OpenhimerLab/CareLite-GPIB/HW/MultiTemp/MultiTemp.png

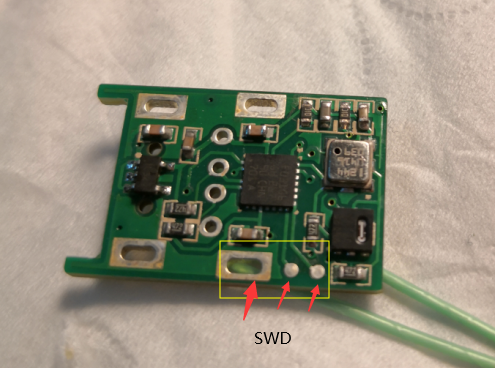
HW/MultiTemp/MultiTemp.png
