OpenhimerLab/CareLite-GPIB/PC Software 1.png

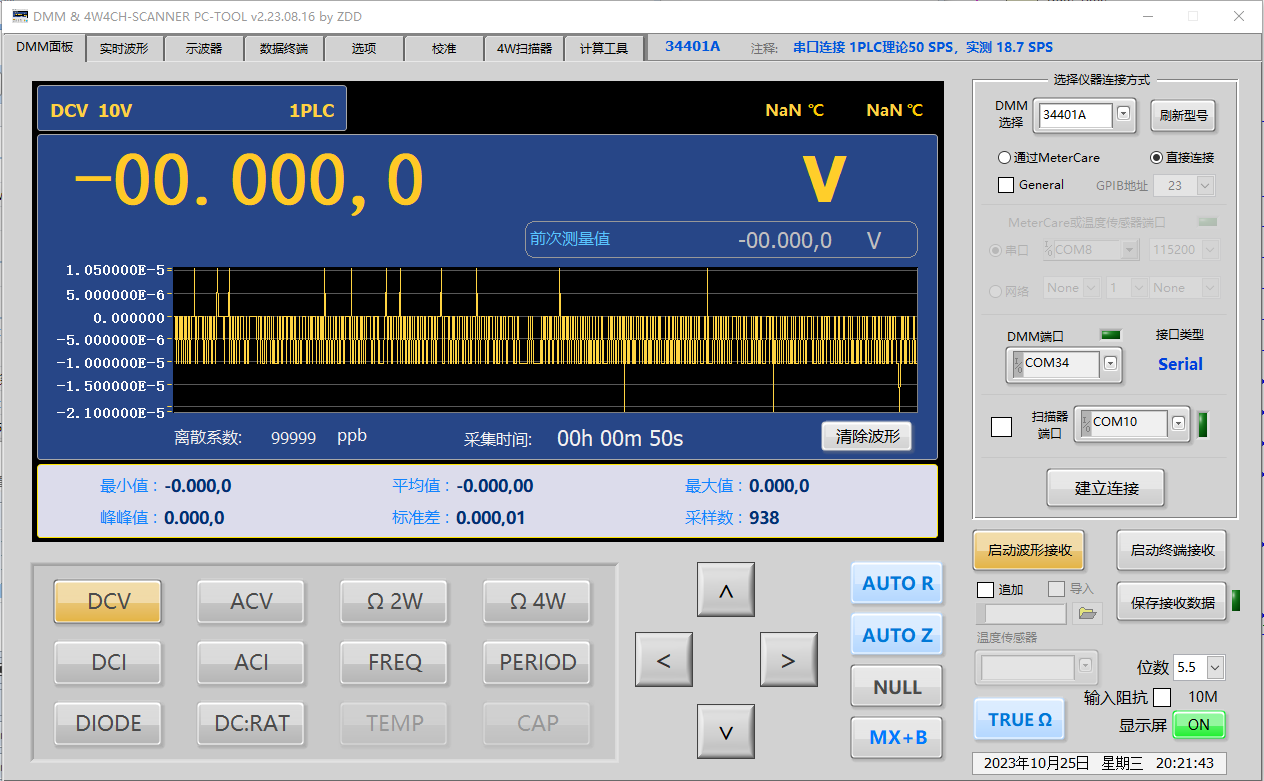
PC Software 1.png
