OpenhimerLab/CareLite-GPIB/PCB4.png

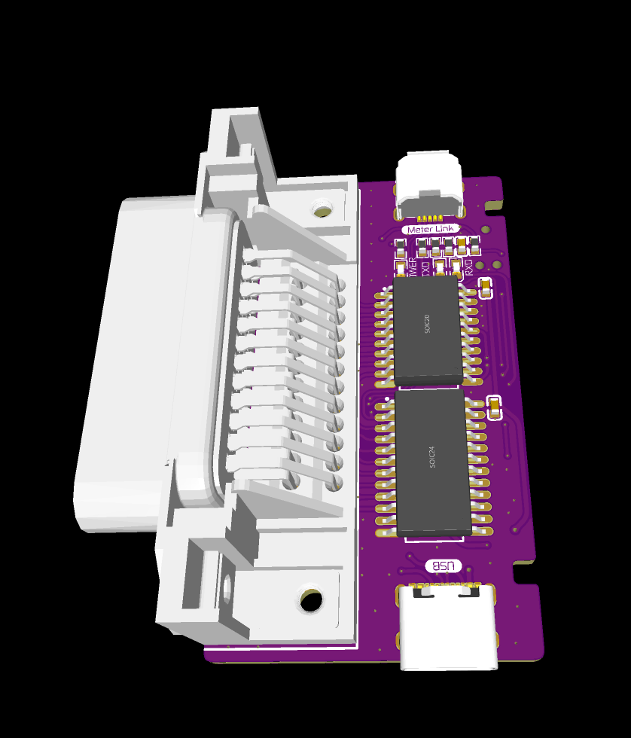
PCB4.png
