OpenhimerLab/CareLite-GPIB/PCB5.png

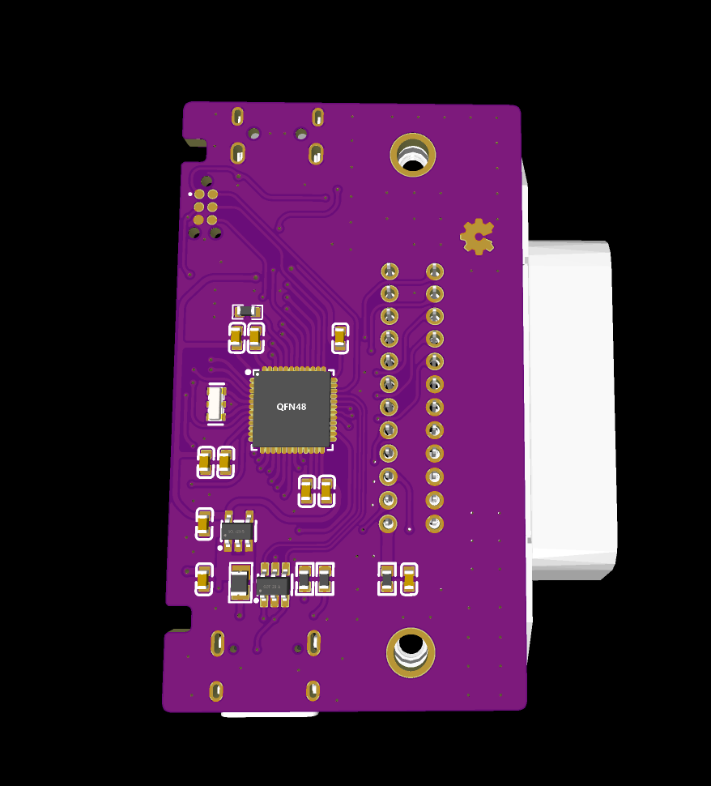
PCB5.png
