OpenhimerLab/CareLite-GPIB/SW/SW in USE 2.jpeg

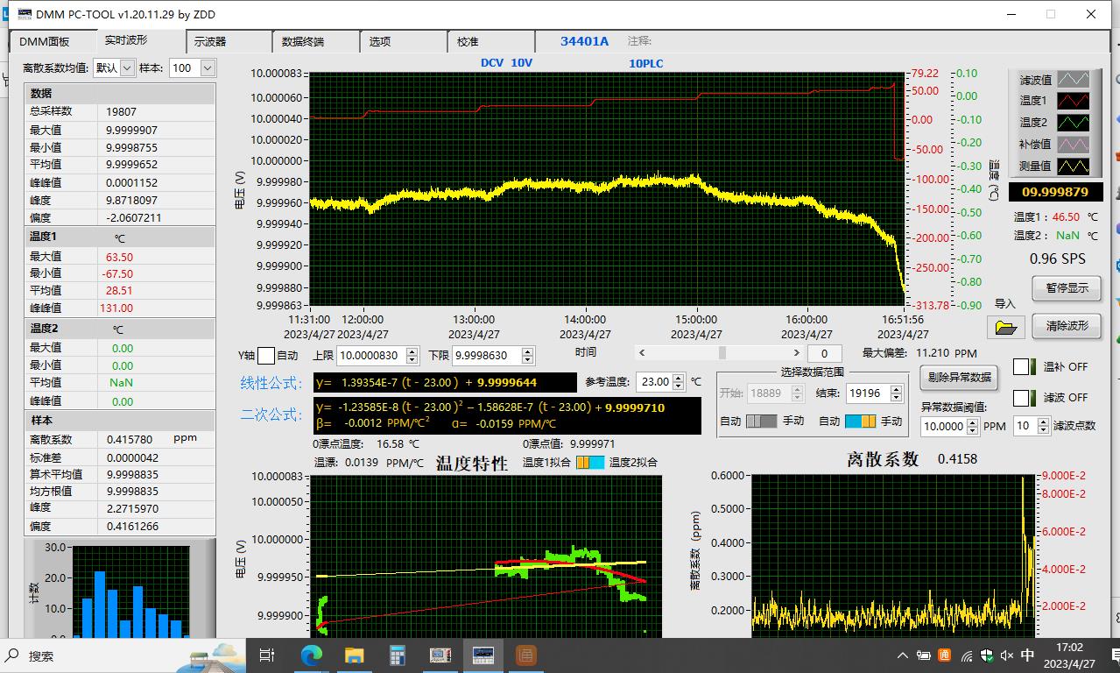
SW/SW in USE 2.jpeg
